BaptisteHudyma/Lamp-Da/Medias/circuit_flash_port.jpeg

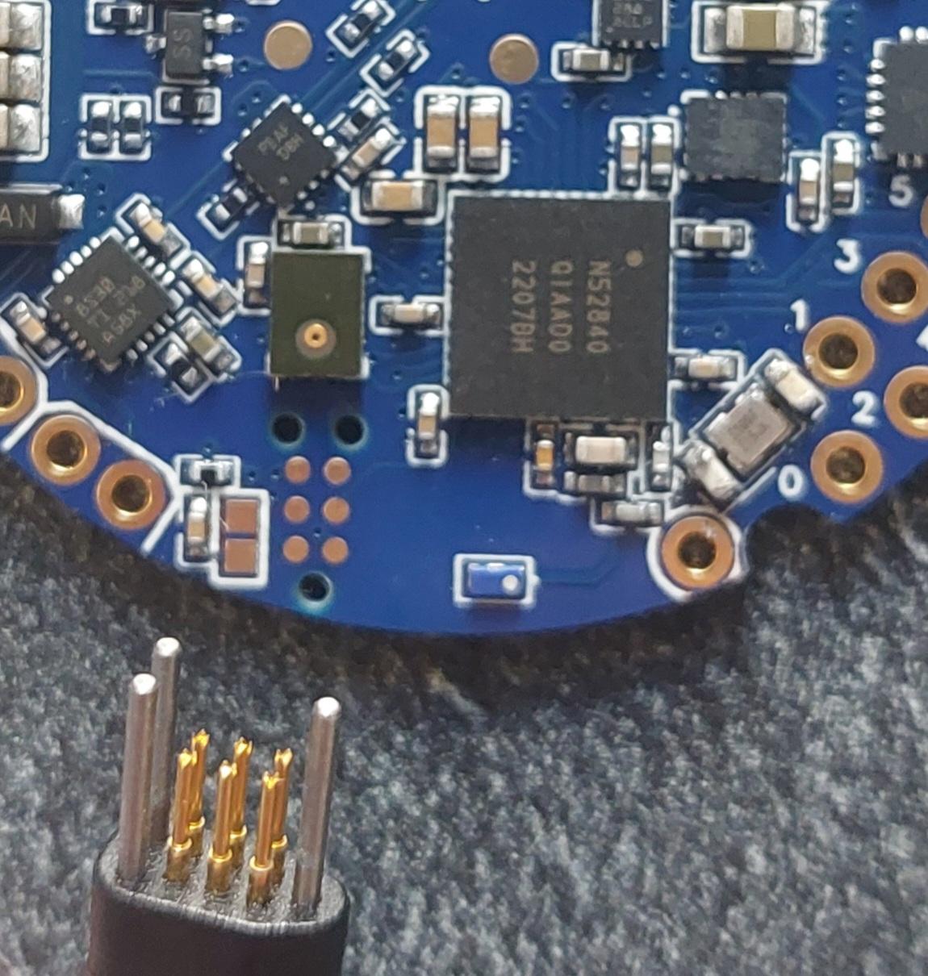
Medias/circuit_flash_port.jpeg
