BaptisteHudyma/Lamp-Da/Medias/Diagramme_commandes-Indexable.png

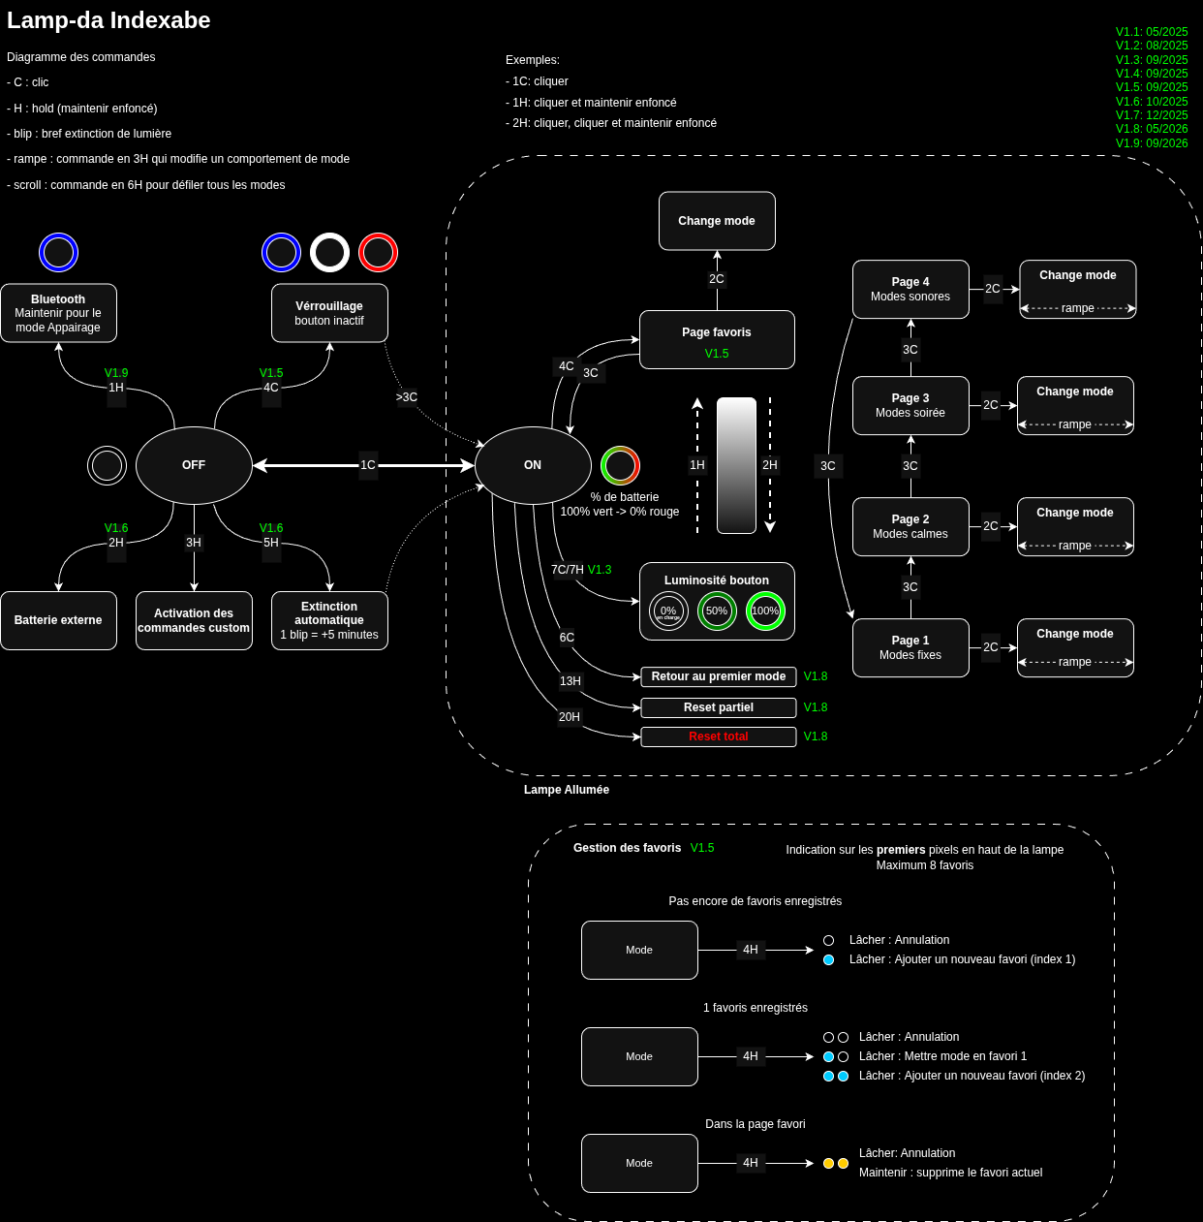
Medias/Diagramme_commandes-Indexable.png
