BaptisteHudyma/Lamp-Da/Medias/raspi_flasher.jpeg

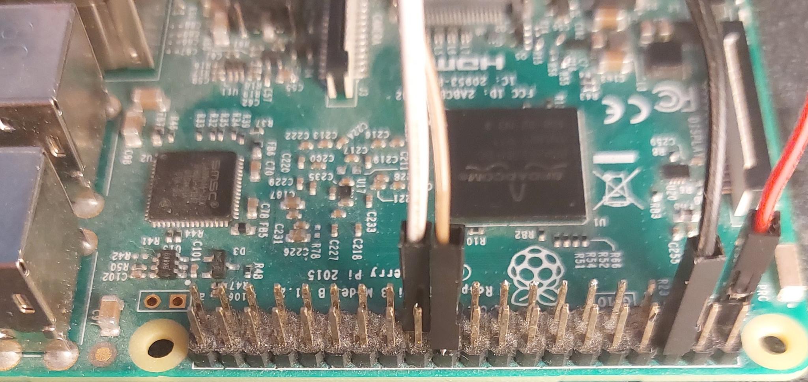
Medias/raspi_flasher.jpeg
