BaptisteHudyma/Lamp-Da/Medias/button_wiring.jpg

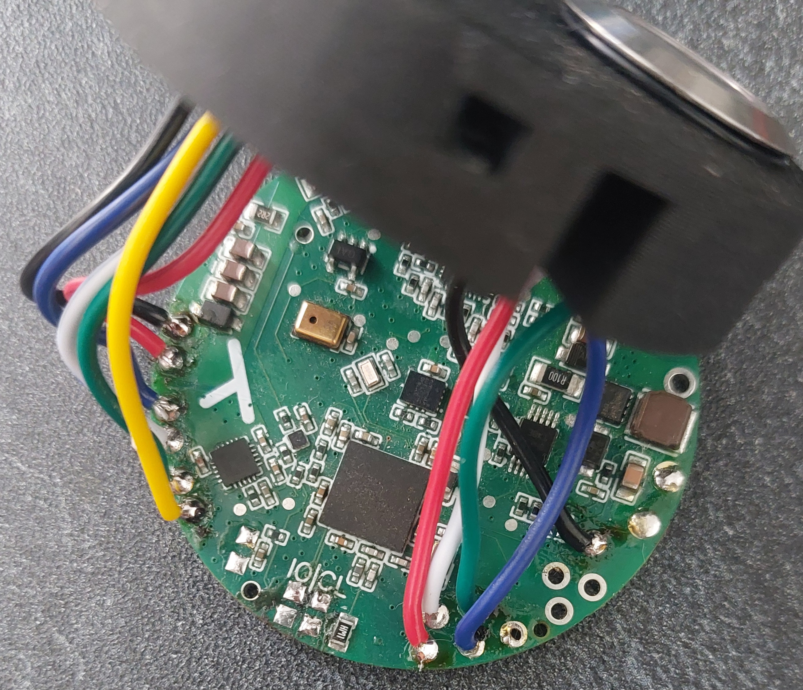
Medias/button_wiring.jpg
