BaptisteHudyma/Lamp-Da/Medias/full_assembly.png

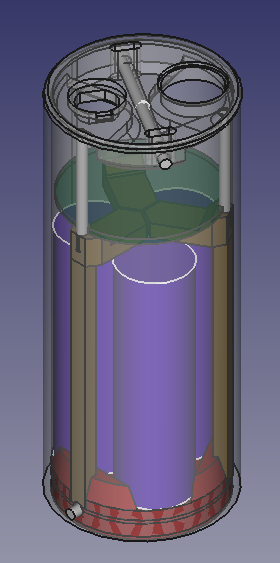
Medias/full_assembly.png
