BaptisteHudyma/Lamp-Da/Medias/printed_assembly.png

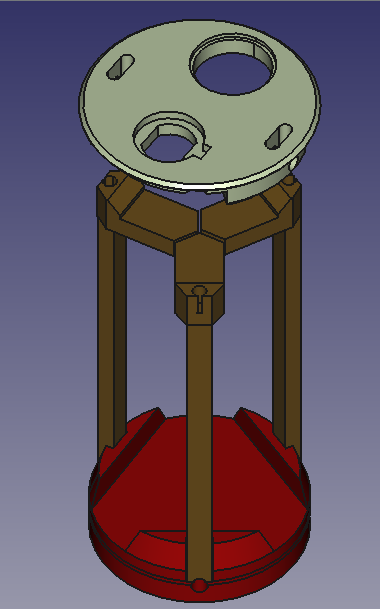
Medias/printed_assembly.png
