BaptisteHudyma/Lamp-Da/src/system/logic/behavior.cpp

#include "behavior.h"

#include <cstdint>

#include "src/system/ext/math8.h"
#include "src/system/ext/noise.h"

#include "src/system/hal/time.h"
#include "src/system/hal/gpio.h"
#include "src/system/hal/i2c.h"
#include "src/system/hal/registers.h"

#include "src/system/bsp/ble.h"
#include "src/system/bsp/text_out.h"

#include "src/system/logic/alerts.h"
#include "src/system/logic/inputs_bluetooth.h"
#include "src/system/logic/inputs.h"
#include "src/system/logic/statistics_handler.h"
#include "src/system/logic/power_handler.h"
#include "src/system/logic/sun_timers.h"

#include "src/system/bsp/indicator.h"
#include "src/system/bsp/filesystem.h"
#include "src/system/bsp/power_gates.h"
#include "src/system/bsp/threads.h"

#include "src/system/component/charger.h"
#include "src/system/component/battery.h"
#include "src/system/component/button.h"
#include "src/system/component/imu.h"
#include "src/system/component/output_power.h"
#include "src/system/component/sound.h"

#include "src/system/utils/colorspace.h"
#include "src/system/utils/constants.h"
#include "src/system/utils/input_output.h"
#include "src/system/utils/time_utils.h"
#include "src/system/utils/utils.h"

#include "src/system/common/state_machine.h"

#include "src/user/functions.h"

namespace lampda {
namespace logic {
namespace behavior {

static constexpr uint32_t cleanSleepKey = utils::hash("cleanSleep");
static constexpr uint32_t brightnessKey = utils::hash("brightness");
static constexpr uint32_t indicatorLevelKey = utils::hash("indLvl");
static constexpr uint32_t isLockoutModeKey = utils::hash("lckMode");
static constexpr uint32_t buttonPinKey = utils::hash("bttPin");
static constexpr uint32_t bluetoothAutoKey = utils::hash("ble");

// time to block turn off since turn on
static constexpr uint32_t SYSTEM_TURN_ON_ALLOW_TURN_OFF_DELAY = 500;
static constexpr uint32_t PRE_CHARGE_STATE_TIMEOUT_ms = 1000;
static constexpr uint32_t PRE_OUTPUT_STATE_TIMEOUT_ms = 1000;

/// bluetooth will power up automatically this number of next boots if user used it
static constexpr uint32_t maxBluetoothAutoActivations = 3;

// timestamp of the system wake up
static uint32_t wakeUpTime = 0;

// pre output light call timing (lamp output starts)
// Starts at system start time
static uint32_t preOutputLightCalled = 0;

// indicates that the system was waken up by voltage on vbus
static bool wokeUpFromVbus_s = false;
// indicates that the output should be turned on/off
static bool isTargetPoweredOn_s = false;
// indicates the error that started the error state
static etl::string<128> errorStateRaisedStr = "";
// indicates the time at which the pre-charge state started
static uint32_t preChargeCalled = 0;
// indicates the  time at which the output state is enabled
static uint32_t lastOutputLightValidTime = 0;
/// keep track of the number of auto bluetooth activation left
static uint32_t bluetoothAutoActivationLeftCount = 0;

// Define the state for the main prog state machine
using BehaviorStates = enum class behavior_t
{
  // handle the start logic
  START_LOGIC,

  // Prepare the charging operations
  PRE_CHARGER_OPERATION,
  // Charging, or usb OTG mode
  CHARGER_OPERATIONS,
  // Prepare the light operation
  PRE_OUTPUT_LIGHT,
  // output voltage on, light the led strip and enable user modes
  OUTPUT_LIGHT,
  // close the output safely
  POST_OUTPUT_LIGHT,

  // shutdown state (when set, the board wil shutdown)
  SHUTDOWN,

  // Should never happen, default state
  ERROR,
};
const char* BehaviorStatesStr[] = {
        "START_LOGIC",
        "PRE_CHARGER_OPERATION",
        "CHARGER_OPERATIONS",
        "PRE_OUTPUT_LIGHT",
        "OUTPUT_LIGHT",
        "POST_OUTPUT_LIGHT",
        "SHUTDOWN",
        "ERROR",
};
// main state machine
common::StateMachine<BehaviorStates> mainMachine(BehaviorStates::START_LOGIC);

// system was powered from vbus power event
bool did_woke_up_from_power() { return wokeUpFromVbus_s; }

// target power on state (not actual state)
bool is_system_should_be_powered() { return isTargetPoweredOn_s; }
void set_power_on() { isTargetPoweredOn_s = true; }
void set_power_off()
{
  // prevent early shutdown when system is just booting, or lamp jst turns on
  if (hal::time_ms() - preOutputLightCalled < SYSTEM_TURN_ON_ALLOW_TURN_OFF_DELAY)
    return;

  isTargetPoweredOn_s = false;
}

void go_to_external_battery_mode() { logic::power::go_to_otg_mode(); }

//
bool is_in_start_logic_state() { return mainMachine.get_state() == BehaviorStates::START_LOGIC; }
bool is_in_output_state() { return mainMachine.get_state() == BehaviorStates::OUTPUT_LIGHT; }
bool is_in_charge_state()
{
  return mainMachine.get_state() == BehaviorStates::CHARGER_OPERATIONS or
         mainMachine.get_state() == BehaviorStates::PRE_CHARGER_OPERATION;
}

namespace timers {

// signal update to user
void sunset_progress_update(const float progress) { user::sunset_timer_update(progress); }
void sunrise_progress_update(const float progress) { user::sunrise_timer_update(progress); }

} // namespace timers

// allow system to be powered if no hardware alert and power is setup
bool can_system_allowed_to_be_powered()
{
  return not(logic::alerts::manager.is_raised(logic::alerts::Type::SYSTEM_IN_ERROR_STATE) or
             not logic::power::is_setup());
}

// return true if vbus is high
bool is_charger_powered() { return ::lampda::component::charger::is_vbus_powered(); }

bool read_parameters()
{
  bool isSuccess = false;
  // load system values in memory
  if (not bsp::filesystem::system::load_from_file())
  {
    logic::alerts::manager.raise(logic::alerts::Type::SYSTEM_SLEEP_SKIPPED);
  }
  else
  {
    isSuccess = true;
    // load statistics first
    statistics::load_from_memory();

    uint32_t wasPutToSleepCleanly = 0;
    const bool isCleanFlagFound = bsp::filesystem::system::get_value(cleanSleepKey, wasPutToSleepCleanly);
    if (not isCleanFlagFound or wasPutToSleepCleanly != 0xDEADBEEF)
    {
      // dirty sleep alert
      logic::alerts::manager.raise(logic::alerts::Type::SYSTEM_SLEEP_SKIPPED);
    }

    uint32_t brightness = 0;
    if (bsp::filesystem::system::get_value(brightnessKey, brightness))
    {
      logic::brightness::update_brightness(brightness, true);
      logic::brightness::update_saved_brightness();
    }

    uint32_t indicatorLevel = 0;
    if (bsp::filesystem::system::get_value(indicatorLevelKey, indicatorLevel))
    {
      logic::indicator::set_brightness_level(indicatorLevel);
    }

    uint32_t isInLockoutMode = 0;
    if (bsp::filesystem::system::get_value(isLockoutModeKey, isInLockoutMode) and isInLockoutMode != 0)
    {
      // system in lockout, raise the alert
      logic::alerts::manager.raise(logic::alerts::Type::SYSTEM_IN_LOCKOUT);
    }

    uint32_t buttonPin = 0;
    if (bsp::filesystem::system::get_value(buttonPinKey, buttonPin) and buttonPin > 0)
    {
      component::button::set_button_pin(static_cast<hal::gpio::DigitalPin::GPIO>(buttonPin));
    }

    // Auto activate bluetooth is needed
    uint32_t bluetoothAutoActivation = 0;
    if (bsp::filesystem::system::get_value(bluetoothAutoKey, bluetoothAutoActivation) and bluetoothAutoActivation > 0)
    {
      bluetoothAutoActivationLeftCount = min<uint32_t>(maxBluetoothAutoActivations, bluetoothAutoActivation - 1);

      // bounded device, advertize but only allow the bounded device, if it exist
      bsp::ble::start_advertising(false);
    }
    else
    {
      bluetoothAutoActivationLeftCount = 0;
    }
  }

  if (not bsp::filesystem::user::load_from_file())
  {
    // We can live without the user parameters, but log it
    bsp::lampda_print("ERROR: Failed to read user parameters");
  }

  // Load the user anyway, there is a default parameter logic in here
  user::read_parameters();

  return isSuccess;
}

void setup_clean_sleep_flag()
{
  // clear clean sleep flag
  bsp::filesystem::system::set_value(cleanSleepKey, 0);
  // write parameters, if a crash happens, we will notice a dirty flag
  bsp::filesystem::system::write_to_file();
}

void write_parameters()
{
  bsp::filesystem::user::clear_cached();

  // write updated statistics
  statistics::write_to_memory();

  bsp::filesystem::system::set_value(cleanSleepKey, 0xDEADBEEF);
  // only save saved brightness, not current
  bsp::filesystem::system::set_value(brightnessKey, logic::brightness::get_saved_brightness());
  bsp::filesystem::system::set_value(indicatorLevelKey, logic::indicator::get_brightness_level());
  // lockout mode always kept, if not deactivated by system
  bsp::filesystem::system::set_value(isLockoutModeKey,
                                     logic::alerts::manager.is_raised(logic::alerts::Type::SYSTEM_IN_LOCKOUT));
  bsp::filesystem::system::set_value(buttonPinKey, static_cast<uint32_t>(component::button::get_button_pin()));

  // if the user used the bluetooth, it will be written here for auto activation
  const uint32_t nextWakeUpWithBluetooth =
          logic::inputs_bluetooth::is_bluetooth_used() ? maxBluetoothAutoActivations : bluetoothAutoActivationLeftCount;
  bsp::filesystem::system::set_value(bluetoothAutoKey, nextWakeUpWithBluetooth);

  // write user parameters
  user::write_parameters();

  // write all
  bsp::filesystem::user::write_to_file();
  bsp::filesystem::system::write_to_file();
}

// user code is running when state is output
bool is_user_code_running() { return mainMachine.get_state() == BehaviorStates::OUTPUT_LIGHT; }

void set_error_state_message(const etl::string<128>& errorMsg)
{
  if (errorStateRaisedStr.empty())
  {
    errorStateRaisedStr = etl::string<128>("\n\t").append(errorMsg);
  }
}
etl::string<128> get_error_state_message()
{
  if (errorStateRaisedStr.empty())
    return "x";
  return errorStateRaisedStr;
}

void go_to_error_state(const etl::string<128>& errorMsg)
{
  statistics::signal_output_off();

  // signal to the system we dont want to turn off until user asked
  // thats better to debug an error
  set_power_on();
  // set error msg
  set_error_state_message(errorMsg);
  // got to error state
  mainMachine.set_state(BehaviorStates::ERROR);
}

namespace internal {

void handle_error_state()
{
  set_error_state_message("Unspecified raised error state reason");

  // not allowed to start, can only be stopped
  // turn off system is needed
  if (not is_system_should_be_powered())
  {
    // got to sleep after the closing operations
    mainMachine.set_state(BehaviorStates::SHUTDOWN);
  }

  // power states go to error too
  logic::power::go_to_error();

  // kick power and user watchdog (prevent reset)
  hal::registers::kick_watchdog(POWER_WATCHDOG_ID);
  hal::registers::kick_watchdog(USER_WATCHDOG_ID);

  // if error state, raise alert
  logic::alerts::manager.raise(logic::alerts::Type::SYSTEM_IN_ERROR_STATE);
}

void handle_start_logic_state()
{
  // set clean flag early on
  setup_clean_sleep_flag();

  // prevent early charging
  logic::power::enable_charge(false);

  // safety for failure of components at startup
  if (not can_system_allowed_to_be_powered())
  {
    go_to_error_state("system not allowed to power on in start logic state");
    return;
  }
  if (logic::power::is_in_error_state())
  {
    go_to_error_state("power system in error state in start logic state");
    return;
  }
  if (not logic::power::is_started())
  {
    // wait until power is started
    hal::delay_ms(1);
    return;
  }

  //
  if (did_woke_up_from_power())
  {
    // signal to the alert manager that we started by power input
    logic::alerts::signal_wake_up_from_charger();

    // start the charge operation
    mainMachine.set_state(BehaviorStates::PRE_CHARGER_OPERATION);
  }
  else
  {
    // small hack: the first button click is never registered, because it happens before the system boots
    set_power_on();
    // start the system normally
    mainMachine.set_state(BehaviorStates::PRE_OUTPUT_LIGHT);
  }
}

void handle_pre_charger_operation_state()
{
  if (logic::power::is_in_error_state())
  {
    go_to_error_state("power system in error state in pre charger operation state");
    return;
  }
  if (hal::time_ms() - mainMachine.get_state_raised_time() > PRE_CHARGE_STATE_TIMEOUT_ms)
  {
    go_to_error_state("pre charger operation failed to toggle to charge");
    return;
  }

  preChargeCalled = hal::time_ms();

  if (not component::battery::can_battery_be_charged())
  {
    // battery cannot be charged
    return;
  }
  if (not logic::alerts::manager.can_use_usb_port())
  {
    // USB port use is locked
    return;
  }

  // force OTG
  if (not logic::power::is_in_otg_mode())
    logic::power::go_to_charger_mode();
  mainMachine.set_state(BehaviorStates::CHARGER_OPERATIONS);
}

void handle_charger_operation_state()
{
  if (logic::power::is_in_error_state())
  {
    go_to_error_state("power system in error state in charger operation state");
    return;
  }

  // pressed the start button, stop charge and start lamp
  if (is_system_should_be_powered())
  {
    // forbid charging
    logic::power::enable_charge(false);
    bsp::threads::yield_this_thread();

    // switch to output mode after the post charge operations
    mainMachine.set_state(BehaviorStates::PRE_OUTPUT_LIGHT);
    return;
  }

  // clear lockout in charge mode
  logic::alerts::manager.clear(logic::alerts::Type::SYSTEM_IN_LOCKOUT);

  // wait a bit after going to charger mode, maybe vbus is bouncing around
  const bool vbusDebounced =
          ::lampda::component::charger::can_use_vbus_power() or (hal::time_ms() - preChargeCalled) > 5000;
  if (vbusDebounced)
  {
    static uint32_t otgDebounce_time = 0;
    if (::lampda::component::charger::get_state().isInOtg)
    {
      otgDebounce_time = hal::time_ms();
    }

    // otg mode
    if ((otgDebounce_time != 0) and (hal::time_ms() - otgDebounce_time) <= 500)
    {
      // do nothing (for now !)
    }
    // no power, shutdown everything
    else if (not is_charger_powered())
    {
      // forbbid charging
      logic::power::enable_charge(false);
      bsp::threads::yield_this_thread();

      // go to sleep after closing the charger
      mainMachine.set_state(BehaviorStates::SHUTDOWN);
      return;
    }
    else
    {
      // enable charge after the debounce
      logic::power::enable_charge(true);
    }
  }
  // else: ignore all
}

bool check_handle_exit_output_mode()
{
  // should go to sleep
  if (not is_system_should_be_powered())
  {
    // cancel both
    logic::sun_timers_cancel_all();

    if (is_charger_powered())
    {
      // charger is plugged, go to charger state
      mainMachine.set_state(BehaviorStates::POST_OUTPUT_LIGHT, 100, BehaviorStates::PRE_CHARGER_OPERATION);
    }
    else
    {
      // got to sleep after the closing operations
      mainMachine.set_state(BehaviorStates::POST_OUTPUT_LIGHT, 1000, BehaviorStates::SHUTDOWN);
    }
    return true;
  }
#ifndef LMBD_SIMULATION
  else if (not component::battery::is_battery_usable_as_power_source())
  {
    logic::sunset_timer.cancel();

    // wait a bit then shutdown
    if (hal::time_ms() - preOutputLightCalled > 3000)
    {
      // indicate we should power the systemm off
      set_power_off();
    }
    return true;
  }
#endif

  return false;
}

void handle_pre_output_light_state()
{
  static bool isMessageDisplayed = false;

  if (logic::power::is_in_error_state())
  {
    go_to_error_state("power system in error state in pre output light state");
    return;
  }
  if (hal::time_ms() - mainMachine.get_state_raised_time() > PRE_OUTPUT_STATE_TIMEOUT_ms)
  {
    go_to_error_state("pre output operation failed to toggle");
    return;
  }

  // power usage is forbidden
  if (not component::battery::is_battery_usable_as_power_source())
  {
    if (not isMessageDisplayed)
    {
      bsp::lampda_print("no output allowed");
      isMessageDisplayed = true;
    }
    // check if we may go to sleep
    check_handle_exit_output_mode();
    return;
  }

  if (logic::alerts::manager.is_raised(logic::alerts::Type::SYSTEM_IN_LOCKOUT))
  {
    if (not isMessageDisplayed)
    {
      bsp::lampda_print("not output in lockout state");
      isMessageDisplayed = true;
    }
    // check if we may go to sleep
    check_handle_exit_output_mode();
    return;
  }

  //
  isMessageDisplayed = false;

  // critical battery level, do not wake up
  if (component::battery::get_battery_minimum_cell_level() <= batteryCritical + 1)
  {
    // alert user of low battery
    for (uint8_t i = 0; i < 10; i++)
    {
      bsp::indicator::set_color(utils::ColorSpace::RED);
      hal::delay_ms(100);
      bsp::indicator::set_color(utils::ColorSpace::BLACK);
      hal::delay_ms(100);
    }

    if (is_charger_powered())
    {
      // go to battery charge instead of shutdown
      isTargetPoweredOn_s = false;
      mainMachine.set_state(BehaviorStates::PRE_CHARGER_OPERATION);
    }
    else
    {
      // battery too low to be powered
      mainMachine.set_state(BehaviorStates::SHUTDOWN);
    }
    return;
  }
  preOutputLightCalled = hal::time_ms();

  logic::power::go_to_output_mode();

  // update brightness with saved brightness
  logic::brightness::update_brightness(logic::brightness::get_saved_brightness());

  // let the user power on the system
  user::power_on_sequence();

  lastOutputLightValidTime = hal::time_ms();

  // this function is executed ONCE
  statistics::signal_output_on();
  mainMachine.set_state(BehaviorStates::OUTPUT_LIGHT);
}

void handle_output_light_state()
{
  if (logic::power::is_in_error_state())
  {
    go_to_error_state("power system in error state in output light state");
    return;
  }

  // shortcut to external battery mode
  if (logic::power::is_in_otg_mode())
  {
    // ignore timing, special case
    isTargetPoweredOn_s = false;
    mainMachine.set_state(BehaviorStates::POST_OUTPUT_LIGHT, 100, BehaviorStates::PRE_CHARGER_OPERATION);
    return;
  }

  static bool waitingForPowerGate_messageDisplayed = true;

  // wait for power gates (and display message when ready)
  if (not ::lampda::bsp::powergates::is_power_gate_enabled() or not logic::power::is_output_mode_ready())
  {
    if (waitingForPowerGate_messageDisplayed)
    {
      bsp::lampda_print("Behavior>Output mode: waiting for power gate");
      waitingForPowerGate_messageDisplayed = false;
    }

    if (hal::time_ms() - lastOutputLightValidTime > 1000)
    {
      etl::string<128> errStr("power gate took too long to switch in output light state ");
      errStr.push_back(static_cast<char>(::lampda::bsp::powergates::is_power_gate_enabled()));
      errStr.push_back(static_cast<char>(logic::power::is_output_mode_ready()));
      go_to_error_state(errStr);
    }
    return;
  }
  waitingForPowerGate_messageDisplayed = true;

  lastOutputLightValidTime = hal::time_ms();

  // normal running loop
  if (not check_handle_exit_output_mode())
  {
    // resume secondary thread
    if (user::should_spawn_thread())
      bsp::threads::resume_thread(bsp::threads::user_taskName);

    // user loop call
    user::loop();

    const auto& chargerState = ::lampda::component::charger::get_state();
    if (chargerState.status == ::lampda::component::charger::Charger_t::ChargerStatus_t::ERROR_BATTERY_MISSING)
    {
      logic::alerts::manager.raise(logic::alerts::Type::BATTERY_MISSING);
    }
  }
}

void handle_post_output_light_state()
{
  // button usermode is kept disabled
  inputs::button_disable_usermode();

  // let the user power off the system
  user::power_off_sequence();
  // write/stability delay
  hal::delay_ms(10);

  // deactivate strip power
  component::outputPower::disable_power_gates(); // close external voltage path
  hal::delay_ms(1);
  component::outputPower::write_voltage(0); // power down

  statistics::signal_output_off();
  mainMachine.skip_timeout();
}

void handle_shutdown_state()
{
  statistics::signal_output_off();

  /**
   * Software shutdown phase
   */

  // Phase 1: bluetooth & com shutdown
  component::button::shutdown();          ///< prevent more button commands
  bsp::ble::stop_bluetooth_advertising(); ///< stop bluetooth
  bsp::ble::shutdown();                   ///< deactivate bluetooth
  hal::delay_ms(20);

  // Phase 2: peripheral shutdown
  component::microphone::disable();
  component::imu::shutdown();
  component::outputPower::write_voltage(0); // power down
  hal::delay_ms(10);

  // Phase 3: power / filesystem
  if (not logic::power::go_to_shutdown())
  {
    // TODO: error ?
  }
  // save the current config to a file
  write_parameters();
  hal::delay_ms(20);
  bsp::filesystem::shutdown();

  // Phase 4: Stop I2C
  for (uint8_t i = 0; i < hal::registers::get_wire_interface_count(); ++i)
  {
    hal::i2c::i2c_turn_off(i);
  }
  hal::delay_ms(10);

  // Phase 5: disable interrupts
  hal::gpio::DigitalPin::detach_all();
  hal::delay_ms(5);

  // Phase 6: Shutdown threads & task stack
  bsp::threads::shutdown();
  hal::delay_ms(10);

  // Phase 7: GPIO deactivation
  // deactivate indicator
  bsp::indicator::set_color(utils::ColorSpace::BLACK);
  hal::delay_ms(1);
  // disable peripherals
  hal::gpio::DigitalPin(hal::gpio::DigitalPin::GPIO::Output_EnableExternalPeripherals).set_high(false);
#ifdef IS_HARDWARE_1_0
  // disable pullup in sleep mode (in V>1.0, done electrically)
  hal::gpio::DigitalPin(hal::gpio::DigitalPin::GPIO::Input_isChargeOk)
          .set_pin_mode(hal::gpio::DigitalPin::Mode::kInput);
  hal::gpio::DigitalPin(hal::gpio::DigitalPin::GPIO::Signal_BatteryBalancerAlert)
          .set_pin_mode(hal::gpio::DigitalPin::Mode::kInput);
#endif
  // disable gates
  hal::gpio::DigitalPin(hal::gpio::DigitalPin::GPIO::Output_EnableVbusGate).set_high(false);
  hal::gpio::DigitalPin(hal::gpio::DigitalPin::GPIO::Output_EnableOutputGate).set_high(false);
  hal::gpio::DigitalPin::deactivate_gpios(); // physically disconnect gpios
  hal::delay_ms(10);

  // Phase 8 : Sleep with wakeup config

  hal::registers::sync_memory_protection();

  // If button is still pressed at this point, we will assume it is stuck pressed and signal a wakeup on release.
  const bool isButtonPressed = component::button::get_button_state().isPressed;
  // power down nrf52.
  // on wake up, it'll start back from the setup phase
  hal::registers::go_to_sleep(component::button::get_button_pin_RAW(), isButtonPressed);

  /*
   * Nothing after this, system is off !
   */

  // if we reach this, the system failed to go to sleep, registers may be broken
  logic::alerts::manager.raise(logic::alerts::Type::SYSTEM_OFF_FAILED);
  go_to_error_state("system failed to sleep");
}

uint32_t get_bluetooth_auto_activation_left() { return bluetoothAutoActivationLeftCount; }

} // namespace internal

/// Handle the behavior states
void state_machine_behavior()
{
  mainMachine.run();
  // if state changed, display the new state
  if (mainMachine.state_just_changed())
  {
    bsp::lampda_print("BEHAVIOR_S_MACH > switched to state %s",
                      BehaviorStatesStr[static_cast<size_t>(mainMachine.get_state())]);
  }

  switch (mainMachine.get_state())
  {
    // strange error state
    case BehaviorStates::ERROR:
      internal::handle_error_state();
      break;
    // called when system starts
    case BehaviorStates::START_LOGIC:
      internal::handle_start_logic_state();
      break;
    // prepare the charger operation
    case BehaviorStates::PRE_CHARGER_OPERATION:
      internal::handle_pre_charger_operation_state();
      break;
    // charge batteries, or power OTG on USB-port
    case BehaviorStates::CHARGER_OPERATIONS:
      internal::handle_charger_operation_state();
      break;
    // prepare the output light
    case BehaviorStates::PRE_OUTPUT_LIGHT:
      internal::handle_pre_output_light_state();
      break;
    // output current to system, handle user inputs
    case BehaviorStates::OUTPUT_LIGHT:
      internal::handle_output_light_state();
      break;
    case BehaviorStates::POST_OUTPUT_LIGHT:
      internal::handle_post_output_light_state();
      break;
    case BehaviorStates::SHUTDOWN:
      internal::handle_shutdown_state();
      break;
    default:
      {
        go_to_error_state("reached state machine default state");
      }
      break;
  }
}

// system was powered by vbus high event
void set_woke_up_from_vbus(const bool wokeUp) { wokeUpFromVbus_s = wokeUp; }

// main behavior loop
void loop()
{
  state_machine_behavior();

  // do not display alerts for the first 500 ms
  const bool shouldIgnoreAlerts = (hal::time_ms() - wakeUpTime) < 500;
  logic::alerts::handle_all(shouldIgnoreAlerts);
  // alert requested an emergency shutdown, do it
  if (logic::alerts::is_request_shutdown())
  {
    bsp::lampda_print("emergency shutdown from alert");
    // just in case, turn off eventual states
    internal::handle_post_output_light_state();
    // shutdown normally
    internal::handle_shutdown_state();
  }

  // only handle those when system is not in alert state
  if (mainMachine.get_state() == BehaviorStates::PRE_OUTPUT_LIGHT or
      mainMachine.get_state() == BehaviorStates::OUTPUT_LIGHT)
  {
    // at any point when the alert is raised, got to power off
    if (logic::alerts::manager.is_raised(logic::alerts::Type::SYSTEM_IN_LOCKOUT) and
        logic::alerts::manager.get_time_since_raised(logic::alerts::Type::SYSTEM_IN_LOCKOUT) > 950)
    {
      const auto& buttonState = component::button::get_button_state();
      const bool isButtonPressed = buttonState.isPressed or buttonState.isLongPressed;
      // shutdown with button pressed starts right back up.
      if (not isButtonPressed)
        behavior::set_power_off();
    }
  }
}

etl::string<32> get_state() { return etl::string<32>(BehaviorStatesStr[static_cast<size_t>(mainMachine.get_state())]); }

} // namespace behavior
} // namespace logic
} // namespace lampda

//
// do not modify (if you do not understand it)
//

#ifdef LMBD_CPP17

const char* ensure_build_canary()
{
#warning "compiling ensure_build_canary"

#ifdef LMBD_LAMP_TYPE__SIMPLE
  return "_lmbd__build_canary__simple";
#endif
#ifdef LMBD_LAMP_TYPE__CCT
  return "_lmbd__build_canary__cct";
#endif
#ifdef LMBD_LAMP_TYPE__INDEXABLE
  return "_lmbd__build_canary__indexable";
#endif
  return (char*)nullptr;
}

#endif
