BaptisteHudyma/Lamp-Da/src/modes/include/hardware/lamp_type.hpp

/*! \file lamp_type.hpp
    \brief Define the main led strip interaction object.
*/

#ifndef MODES_HARDWARE_LAMP_TYPE_HPP
#define MODES_HARDWARE_LAMP_TYPE_HPP

#include <cstdint>
#include <cstring>

#include "src/compile.h"
#include "src/user/constants.h"

#include "src/system/component/output_power.h"
#include "src/system/component/sound.h"

#ifdef LMBD_LAMP_TYPE__INDEXABLE
#include "src/system/component/strip.h"
#endif

#include "src/system/hal/time.h"

#include "src/system/bsp/text_out.h"

#include "src/system/logic/brightness_handle.h"

#include "src/system/utils/assert.h"
#include "src/system/utils/constants.h"
#include "src/system/utils/utils.h"

#include "src/system/common/curves.h"

#include "src/system/ext/math8.h"

#include "src/modes/include/compile.hpp"
#include "src/modes/include/hardware/coordinates.hpp"

#include "src/modes/include/colors/utils.hpp"
#include "src/modes/include/colors/palettes.hpp"

namespace lampda::modes {

struct XYTy
{
  uint16_t x; ///< x 2D led grid coordinates
  uint16_t y; ///< y 2D led grid coordinates
};

/// convert grid coordinates to strip index
static constexpr uint16_t to_strip(uint16_t, uint16_t);
/// convert strip index to grid coordinates
static constexpr XYTy strip_to_XY(uint16_t n);

struct HelixXYZTy
{
  float x; ///< x 3D mm coordinates
  float y; ///< y 3D mm coordinates
  float z; ///< z 3D mm coordinates
};

/// convert strip index to 3D coordinates
static constexpr HelixXYZTy strip_to_helix(int16_t n);

/// convert strip index to 3D coordinates, without checks on led index.
/// This allows to use 3D coordinates out of the lamp body
static constexpr HelixXYZTy strip_to_helix_unconstraint(const int16_t n);
/// True if the given strip index is a valid one
static constexpr bool is_led_index_valid(const int16_t ledIndex);
/// True if the given led index is out of bounds
static constexpr bool is_lamp_coordinate_out_of_bounds(const float angle_rad, const float z);

/**
 * \brief convert a lamp coordinate to a led index
 */
static constexpr uint16_t to_led_index(const float angle_rad, const float z);

/**
 * \brief convert a lamp coordinate to a led index, the result can be an index out of the lamp body
 */
static constexpr int16_t to_led_index_no_bounds(const float angle_rad, const float z);

} // namespace lampda::modes

/// Provide interface to the physical hardware and other facilities
namespace lampda::modes::hardware {

/** \brief Enumeration to write code working with all lamp types
 *
 * See LampTy::flavor and its usage
 */
enum class LampTypes : uint8_t
{
  simple,    ///< Equivalent to LMBD_LAMP_TYPE__SIMPLE
  cct,       ///< Equivalent to LMBD_LAMP_TYPE__CCT
  indexable, ///< Equivalent to LMBD_LAMP_TYPE__INDEXABLE
};

#ifdef LMBD_LAMP_TYPE__SIMPLE
static constexpr LampTypes _lampType = LampTypes::simple;
#endif

#ifdef LMBD_LAMP_TYPE__CCT
static constexpr LampTypes _lampType = LampTypes::cct;
#endif

#ifdef LMBD_LAMP_TYPE__INDEXABLE
static constexpr LampTypes _lampType = LampTypes::indexable;
#endif

/// Currently implemented lamp type, defined at compile-time by the user
static constexpr LampTypes lampType = _lampType;

/** \brief Main interface between the user and the hardware of the lamp
 *
 * TODO: write recipes for best practices when doing Simple/CCT/Indexable
 */
struct LampTy
{
  //
  // state managed by manager
  //

  /// Store a display config
  struct LampConfig
  {
    uint16_t skipFirstLedsForEffect = 0; ///< Skip duration
    uint16_t skipFirstLedsForAmount = 0; ///< Skip the first N leds
  };

  /// store a display configuration
  LampConfig config;

  //
  // private constructors
  //

#ifdef LMBD_LAMP_TYPE__INDEXABLE
private:
  static constexpr float _fwidth = stripXCoordinates;                    ///< \private
  static constexpr float _fheight = stripYCoordinates;                   ///< \private
  static constexpr uint16_t _width = floor(_fwidth);                     ///< \private
  static constexpr uint16_t _height = floor(_fheight);                   ///< \private
  static constexpr uint16_t _ledCount = LED_COUNT;                       ///< \private
  static constexpr uint16_t _nbBuffers = stripNbBuffers;                 ///< \private
  static constexpr float _lampBodyRadius_mm = lampda::lampBodyRadius_mm; ///< \private
  static constexpr float _ledStripWidth_mm = lampda::ledStripWidth_mm;   ///< \private
  static constexpr float _ledStripLength_mm = lampda::ledStripLength_mm; ///< \private
  static constexpr float _ledByMeter = lampda::ledByMeter;               ///< \private
  component::LedStrip& strip;                                            ///< \private

  /// \private oversized buffer size to account for "overflowing" LEDs
  static constexpr uint16_t _safeBufSize = (_width + 1) * (_height + 1);

  /// Type for a uint32_t buffer of exactly ledCount length
  using BufferTy = std::array<uint32_t, _ledCount>;
  // using BufferTy = std::array<uint32_t, _safeBufSize>;

  LampTy() = delete;                         ///< \private
  LampTy(const LampTy&) = delete;            ///< \private
  LampTy& operator=(const LampTy&) = delete; ///< \private

public:
  /// \private Constructor used to wrap strip if needed
  LMBD_INLINE LampTy(component::LedStrip& strip) : config {}, strip {strip}, now {0}, tick {0}, raw_frame_count {0} {}
#else
private:
  // (placeholder values to avoid bad fails on misuse)
  static constexpr float _fwidth = 23.5451;          ///< \private
  static constexpr float _fheight = 22.51;           ///< \private
  static constexpr uint16_t _width = 23;             ///< \private
  static constexpr uint16_t _height = 22;            ///< \private
  static constexpr uint16_t _ledCount = 530;         ///< \private
  static constexpr uint16_t _nbBuffers = 3;          ///< \private
  static constexpr float _lampBodyRadius_mm = 25.0f; ///< \private
  static constexpr float _ledStripWidth_mm = 5.2f;   ///< \private
  static constexpr float _ledStripLength_mm = 25.0f; ///< \private
  static constexpr float _ledByMeter = 160.0f;       ///< \private

  /// \private oversized buffer size to account for "overflowing" LEDs
  static constexpr uint16_t _safeBufSize = (_width + 1) * (_height + 1);

  /// Type for a uint32_t buffer of exactly ledCount length
  using BufferTy = std::array<uint32_t, _ledCount>;
  // using BufferTy = std::array<uint32_t, _safeBufSize>;

  LampTy(const LampTy&) = delete;            ///< \private
  LampTy& operator=(const LampTy&) = delete; ///< \private

  struct LedStrip ///< \private
  {
    BufferTy _buffers[_nbBuffers];
    COLOR _colors[_ledCount]; // !! slighly smaller than buffers in _buffers !!

    void begin();
    void show();
    void show_now();
    void signal_display();
    void setBrightness(brightness_t);
    uint8_t getBrightness();
    void setPixelColor(uint16_t, uint32_t);
    uint32_t getPixelColor(uint16_t);
  };
  LedStrip fakeStrip; ///< \private
  LedStrip& strip;    ///< \private

public:
  /// \private Constructor used to wrap strip if needed
  LMBD_INLINE LampTy() : config {}, fakeStrip {}, strip {fakeStrip}, now {0}, tick {0}, raw_frame_count {0} {}
#endif

  //
  // private API
  //

  /// \private (refresh internal const tick variable)
  void LMBD_INLINE refresh_tick_value()
  {
    uint32_t* writeable_now = const_cast<uint32_t*>(&now);
    *writeable_now = hal::time_ms();

    uint32_t* writable_tick = const_cast<uint32_t*>(&tick);
    *writable_tick = now / frameDurationMs;

    uint32_t* writable_frame_count = const_cast<uint32_t*>(&raw_frame_count);
    *writable_frame_count += 1; // monotonous
  }

  /** \private Startup sequence of the lamp from a powered-off state
   *
   * In order:
   *  - call lamp.begin()
   *  - call lamp.clear()
   *  - call lamp.show()
   *  - call lamp.setBrightness(get_brightness(), true, true)
   *
   * Supports all flavors, even if most steps are no-op if not indexable
   */
  void LMBD_INLINE startup()
  {
    // set output voltage for leds that will not change voltage
    if (stripInputMinVoltage_mV == stripInputMaxVoltage_mV)
      component::outputPower::write_voltage(stripInputMaxVoltage_mV);

    begin();
    clear();
    show_now();
    setBrightness(logic::brightness::get_saved_brightness(), true, true);
    align_internal_to_system_brightness();
  }

  /** \private Does necessary work to setup lamp from a powered-off state
   *
   * If flavor is LampTypes::indexable then:
   *  - call the "begin" method of the LED strip to let it setup itself
   *
   * Or else, subject to change as other flavors are integrated:
   *  - does nothing
   */
  void LMBD_INLINE begin()
  {
    if constexpr (flavor == LampTypes::indexable)
    {
      strip.begin();
    }
    else
    {
      // (this is optimized out, and is essentially no-op for other flavors)
      assert(true);
    }
  }

  /** \private Does necessary work to display not-yet-shown lamp changes
   *
   * If LampTy::flavor is LampTypes::indexable then:
   *  - update the output of the lamp with currently buffered changes
   *
   * Or else, subject to change as other flavors are integrated:
   *  - does nothing
   */
  void LMBD_INLINE show()
  {
    if constexpr (flavor == LampTypes::indexable)
    {
      strip.show();
    }
    else
    {
      // (this is optimized out, and is essentially no-op for other flavors)
      assert(true);
    }
  }

  /** \private Does necessary work to display not-yet-shown lamp changes
   *
   * If LampTy::flavor is LampTypes::indexable then:
   *  - update the output of the lamp with currently buffered changes IMMEDIATLY
   *
   * Or else, subject to change as other flavors are integrated:
   *  - does nothing
   */
  void LMBD_INLINE show_now()
  {
    if constexpr (flavor == LampTypes::indexable)
    {
      strip.show_now();
    }
    else
    {
      // (this is optimized out, and is essentially no-op for other flavors)
      assert(true);
    }
  }

  /** \private Signal to underlying strip that things are ready to be displayed
   *
   * If LampTy::flavor is LampTypes::indexable then:
   *  - call the .signal_display() method of the underlying strip object
   *
   * Or else, subject to change as other flavors are integrated:
   *  - does nothing
   */
  void LMBD_INLINE signal_display()
  {
    if constexpr (flavor == LampTypes::indexable)
    {
      strip.signal_display();
    }
    else
    {
      // (this is optimized out, and is essentially no-op for other flavors)
      assert(true);
    }
  }

  //
  // public constants
  //

  /// Which lamp flavor is currently used by the implementation?
  static constexpr LampTypes flavor = lampType;

  /// Hardward try to call .loop() every frameDurationMs (12ms for 83.3fps)
  static constexpr uint32_t frameDurationMs = MAIN_LOOP_UPDATE_PERIOD_MS;

#ifndef LMBD_LAMP_TYPE__INDEXABLE_IS_HD
  // (we have 12ms and 83.3fps values to be updated in this file)
  static_assert(frameDurationMs == 12, "Update the documentation of .tick :)");
#endif

  /// Limit mode-requested brightness changes to one every few frames
  static constexpr uint32_t brightnessDurationMs = frameDurationMs * 2;

  /** \brief (indexable) Count of indexable LEDs on the lamp
   *
   * Equal to \p LED_COUNT if LampTypes::indexable or else 512
   */
  static constexpr uint16_t ledCount = _ledCount;

  /** \brief (indexable) Width of "pixel space" w/ lamp taken as a LED matrix
   *
   * This width equals the smallest maximal X coordinate for which all rows
   * are fully displayed on the lamp taken as an "XY-display" LED matrix.
   *
   * All rows are of length of at least \p maxWidth but some will be of length
   * \p maxOverflowWidth depending on the exact diameter of the lamp and
   * density of the LED strip.
   *
   * Equal to \p stripXCoordinates (floor) if LampTypes::indexable or else 23
   */
  static constexpr uint16_t maxWidth = _width;

  /// Width as a precise floating point number, equal to \p stripXCoordinates
  static constexpr float maxWidthFloat = _fwidth;

  /// Larger width, taken as the absolute maximum X coordinate on all rows
  static constexpr uint16_t maxOverflowWidth = maxWidth + 1;

  /** \brief (indexable) Height of "pixel space" w/ lamp taken as a LED matrix
   *
   * This height equals the largest Y coordinate for which a full \p maxWidth
   * row can be displayed, the last row at coordinate \p maxOverflowHeight
   * being likely to be truncated depending on the exact diameter of the lamp
   * and density of the LED strip.
   *
   * The largest LED matrix fully displayed on the lamp taken as an XY screen
   * display is thus of width \p maxWidth and height \p maxHeight leaving out
   * some "outside" of the default display size.
   *
   * Equal to \p stripYCoordinates (floor) if LampTypes::indexable or else 22
   */
  static constexpr uint16_t maxHeight = _height;

  /// Height as a precise floating point number, equal to \p stripYCoordinates
  static constexpr float maxHeightFloat = _fheight;

  /// Larger height, taken as the absolute maximum Y coordinate, overflowing
  static constexpr uint16_t maxOverflowHeight = maxHeight + 1;

  /// \private Exact visual (X,Y) shift for each row of LED rolled around lamp
  static constexpr float shiftPerTurn = _fwidth - floor(_fwidth - 0.0001);

  /// \private Fixed "period" of the (X,Y) shift for each row (set at 2)
  static constexpr uint16_t shiftPeriod = 2;

  /// (while shifting every shiftPeriod, we have a residue accumulating)
  static constexpr float _invShiftResidue = shiftPeriod * (_fwidth - floor(_fwidth - 0.0001));

  /// \private Approximate (broken) visual coordinate X-shift every \p shiftResidue rows
  static constexpr uint16_t shiftResidue = 100.0 / abs(100.0 * _invShiftResidue - 100.0);

  /// \private All **exact** "residue" / amount of X-shift given the Y coordinate
  static constexpr auto allResiduesY = details::computeResidues<maxOverflowHeight>(_fwidth);

  /// \private Is row at Y coordinate slightly longer than \p maxWidth or not?
  static constexpr auto allDeltaResiduesY = details::computeDeltaResidues<maxOverflowHeight>(_fwidth);

  /// \private Return **total** exact accumulated X-shift residue, accross all previous rows
  static constexpr auto extraShiftResiduesY = details::computeExtraShiftResidues<maxOverflowHeight>(_fwidth);

  /// \private Last (final) total X-shift at the end, all row shifts together
  static constexpr int extraShiftTotal = extraShiftResiduesY[maxOverflowHeight - 1];

  /// real radius of the lamp body
  static constexpr float lampBodyRadius_mm = _lampBodyRadius_mm;

  /// real size of the led strip in use
  static constexpr float ledStripWidth_mm = _ledStripWidth_mm;
  /// Copy the led strip lenght
  static constexpr float ledStripLength_mm = _ledStripLength_mm;

  /// number of led per meters of strip used
  static constexpr float ledByMeter = _ledByMeter;

  /// Number of leds per one turn of led strip
  static constexpr float ledSize_mm = 1000.0f / ledByMeter;
  /// Computation of the lamp body circumpherence
  static constexpr float lampBodyCircumpherence_mm = c_TWO_PI * lampBodyRadius_mm;
  /// Computation of the led count per turns
  static constexpr float ledPerTurns = lampBodyCircumpherence_mm / ledSize_mm;
  /// Computation of the lamp height
  static constexpr float lampHeight_mm = ledStripWidth_mm * ledCount / ledPerTurns;

  /** \brief (indexable) Number of color buffers available for direct access
   *
   * Equal to \p stripNbBuffers if LampTypes::indexable or else 2
   */
  static constexpr uint8_t nbBuffers = _nbBuffers;

  //
  // public helpers
  //

  /** \brief (indexable) Return a led count in 0-ledCount scaled by \p scale
   *
   * Supports:
   *    - from float (0-1) to count (0-ledCount)
   *    - from uint8_t (0-255) to count (0-ledCount)
   */
  template<typename T> static constexpr LMBD_INLINE uint16_t toLedCount(T scale)
  {
    if constexpr (std::is_same_v<T, float>)
    {
      assert(scale <= 1.0 && "scale is 0-1");
      return ledCount * scale;
    }
    else if constexpr (std::is_same_v<T, uint8_t>)
    {
      uint32_t scaled = ledCount * scale;
      return scaled / 256;
    }
    else
    {
      static_assert(std::is_same_v<T, std::false_type>, "Invalid type, either float or uint8_t required!");
      return 0;
    }
  }

  //
  // public API
  //

  /** \brief Clear lamp to a clean state
   *
   * If LampTy::flavor is LampTypes::indexable then:
   *  - clear LED strip with black pixels
   *
   * Or else, for interoperability:
   *  - does nothing
   */
  void LMBD_INLINE clear()
  {
    if constexpr (flavor == LampTypes::indexable)
    {
      for (uint16_t i = 0; i < ledCount; ++i)
      {
        setPixelColor(i, colors::Black);
      }
    }
    else
    {
      // (this is optimized out, and is essentially no-op for other flavors)
      assert(true);
    }
  }

  /** \brief blip the power gate for set time
   *
   * If LampTy::flavor is LampTypes::indexable then:
   *  - clear LED strip with black pixels
   * Else
   *  - disable output power for a duration
   */
  void LMBD_INLINE blip(const uint32_t duration)
  {
    if constexpr (flavor == LampTypes::indexable)
    {
      // disable strip temporarily
      // should be reactivated by the manager
      tempBrightness(0);
    }
    else
    {
      component::outputPower::blip(duration);
    }
  }

  /**
   * \brief Cancel the ongoing blip, if any
   */
  void LMBD_INLINE cancel_blip() const { return component::outputPower::cancel_blip(); }

  /**
   * \brief return true if the output is in a blip state
   */
  bool LMBD_INLINE is_bliping() const { return component::outputPower::is_bliping(); }

  /** \brief Set brightness of the lamp
   *
   * Several behaviors:
   *  - by default, do not call user callbacks to avoid re-entry
   *  - by default, do call global brightness update handler (see brightness_handle.h)
   *  - by default, do NOT save brightness using "previous_brightness_update"
   *  - also set the brightness in underlying strip object, if necessary
   *
   * Thus:
   *  - if \p skipCallbacks is false, do call user callbacks w/ re-entry risks
   *  - if \p skipUpdateBrightness is true, only set strip object brightness,
   *    or do nothing if LampTy::flavor is not LampTypes::indexable
   *  - if \p updateSavedBrightess is true, save brightness and next time
   *    user navigate brightness, use it as starting point (see tempBrightness)
   *
   * Note that calls to `logic::brightness::update_brightness` are throttled to once
   * in every 50ms to avoid freezing user brightness navigation.
   *
   * Note that \p skipUpdateBrightness implies \p skipCallbacks implicitly
   */
  void LMBD_INLINE setBrightness(const brightness_t newBrightness,
                                 const bool skipCallbacks = true,
                                 const bool skipUpdateBrightness = false,
                                 const bool updateSavedBrightess = false)
  {
    assert((skipCallbacks || !skipUpdateBrightness) && "implicit callback skip!");

    // invalid call, fallback to enforcing
    if (newBrightness > ::lampda::brightness::absoluteMaximumBrightness)
    {
      enforce_internal_brightness_limits();
      return;
    }

    // force update if we are getting lower and lower
    if (!skipUpdateBrightness or newBrightness > getMaxBrightness())
    {
      // store the new temporary
      temporary_brightness = min<brightness_t>(newBrightness, getMaxBrightness());

      uint32_t last = logic::brightness::when_last_update_brightness();
      if ((this->now - last) > brightnessDurationMs)
        logic::brightness::update_brightness(temporary_brightness, skipCallbacks);
    }
    // if necessary, update the saved version
    if (updateSavedBrightess)
    {
      saved_brightness = min<brightness_t>(static_cast<brightness_t>(temporary_brightness), getMaxBrightness());
    }

    // USE THE BRIGHTNESS VALUE AFTER THE UPDATE
    // brightness can be limited by the system, so do not use the raw brightness
    const auto trueNewBrightness = logic::brightness::get_brightness();

    if constexpr (flavor == LampTypes::indexable)
    {
#ifndef LMBD_LAMP_TYPE__INDEXABLE
      static constexpr uint8_t minimumAllowedBrightness = 5;
#else
      static constexpr uint8_t minimumAllowedBrightness = ::lampda::minimumAllowedBrightness_8;
#endif
      using curve_t = common::curves::LinearCurve<brightness_t, uint8_t>;
      static curve_t brightnessCurve = ::lampda::common::curves::make_linear_curve(
              curve_t::point_t {0, minimumAllowedBrightness},
              curve_t::point_t {::lampda::brightness::absoluteMaximumBrightness, 255});

      /// @warning: this is actually heavy to run
      strip.setBrightness(brightnessCurve.sample(trueNewBrightness));
    }

    if constexpr (flavor == LampTypes::simple)
    {
      const auto trueMaxBrightness = logic::brightness::get_max_brightness();

      // This is kind of a hack to detect that the user did this call
      // using the known user call signature
      const bool isUserCall = skipCallbacks and skipUpdateBrightness and not updateSavedBrightess;

      // display an output blip on max brightness reached
      if (isUserCall and trueNewBrightness >= trueMaxBrightness)
      {
        component::outputPower::blip(50); // blip
      }

      using curve_t = common::curves::ExponentialCurve<brightness_t, uint16_t>;
      static curve_t brightnessCurve(
              curve_t::point_t {0, stripInputMinVoltage_mV},
              curve_t::point_t {::lampda::brightness::absoluteMaximumBrightness, stripInputMaxVoltage_mV},
              1.0);

      component::outputPower::write_voltage(round(brightnessCurve.sample(trueNewBrightness)));
    }
  }

  /// Special call to update the internal brightness values to the system brightness
  void align_internal_to_system_brightness()
  {
    saved_brightness = min<brightness_t>(logic::brightness::get_saved_brightness(), getMaxBrightness());
    temporary_brightness = saved_brightness;
  }

  /// Enforce the brightness limits, if getMaxBrightness changed. Will call \ref setBrightness
  void enforce_internal_brightness_limits()
  {
    const auto maxAllowedBrightness = getMaxBrightness();
    const brightness_t new_saved_brightness =
            min<brightness_t>(static_cast<brightness_t>(saved_brightness), maxAllowedBrightness);
    const brightness_t new_temporary_brightness =
            min<brightness_t>(static_cast<brightness_t>(temporary_brightness), maxAllowedBrightness);

    const bool isChanged = new_saved_brightness != saved_brightness or new_temporary_brightness != temporary_brightness;
    if (isChanged)
    {
      saved_brightness = new_saved_brightness;
      temporary_brightness = new_temporary_brightness;

      setBrightness(temporary_brightness);
    }
  }

  /**
   * \brief Return the actual allowed maximum brightness
   */
  brightness_t LMBD_INLINE getMaxBrightness() const { return logic::brightness::get_max_user_brightness(); }

  /**
   * \brief Temporarily set brightness, without affecting brightness navigation
   *
   * Skip callbacks.
   *
   * Set brightness, without affecting internal brightness navigation state,
   * which imply that next time an user increases / lowers brightness, it
   * starts again from another internal "previously saved" brightness.
   *
   * Equivalent to ``setBrightness(true, false, false)``
   */
  void LMBD_INLINE tempBrightness(const brightness_t brightness)
  {
    brightness_t current = getBrightness();
    if (current != brightness)
      setBrightness(brightness, true, false, false);
  }

  /**
   * \brief Jump to brightness, affecting the next brightness navigation
   *
   * Skip callbacks.
   *
   * Set brightness, affecting internal brightness navigation state,
   * which imply that next time an user increases / lowers brightness, it
   * starts again from the provided brightness.
   *
   * Equivalent to ``setBrightness(true, false, true)``
   */
  void LMBD_INLINE jumpBrightness(const brightness_t brightness) { setBrightness(brightness, true, false, true); }

  /**
   * \brief Get brightness of the lamp
   *
   * If \p readPreviousBrightness is true, return the internally saved
   * brightness state, used for user navigation of brightness.
   */
  brightness_t LMBD_INLINE getBrightness(const bool readPreviousBrightness = false)
  {
    if (readPreviousBrightness)
      return saved_brightness;
    else
      return temporary_brightness;
  }

  /// Alias for ``getBrightness(true)``
  brightness_t LMBD_INLINE getSavedBrightness() { return getBrightness(true); }

  /// Reset brightness to internal saved brightness, skip callbacks
  void LMBD_INLINE restoreBrightness()
  {
    const brightness_t current = getBrightness();
    const brightness_t saved = getSavedBrightness();

    if (current != saved)
      setBrightness(saved, true, false, false);
  }

  /** \brief Fade currently displayed content by \p fadeBy units
   *
   * If LampTy::flavor is LampTypes::indexable then:
   *  - do not change brightness, only scale color of individual LEDs
   *
   * Or else, for other flavors of lamp:
   *  - reduce brightness by \p fadeBy floored at zero
   */
  void LMBD_INLINE fadeToBlackBy(uint8_t fadeBy)
  {
    if constexpr (flavor == LampTypes::indexable)
    {
      if (fadeBy == 0)
        return; // optimization - no scaling to apply

      for (uint16_t i = 0; i < ledCount; ++i)
      {
        const uint32_t c = getPixelColor(i);
        setPixelColor(i, colors::fade(c, 255 - fadeBy));
      }
    }
    else
    {
      uint8_t brightness = getBrightness();
      brightness = (brightness < fadeBy) ? 0 : brightness - fadeBy;
      setBrightness(brightness);
    }
  }

  /** \brief Blur currently displayed content by \p blurBy units
   * /!\ Only applied along the strip, not in 2D /!\
   *
   * If LampTy::flavor is LampTypes::indexable then:
   *  - do not change brightness, only scale color of individual LEDs
   *
   * Or else, for other flavors of lamp:
   *  - blue colors by \p blurBy floored at zero
   */
  void LMBD_INLINE blur(uint8_t blurBy)
  {
    if (blurBy == 0)
      return; // optimization: 0 means "don't blur"
    uint8_t keep = 255 - blurBy;
    uint8_t seep = blurBy >> 1;

    uint32_t carryover = 0;
    for (unsigned i = 0; i < ledCount; i++)
    {
      uint32_t cur = getPixelColor(i);
      uint32_t c = cur;
      uint32_t part = colors::fade<false>(c, seep);
      cur = colors::add<true>(colors::fade<false>(c, keep), carryover);
      if (i > 0)
      {
        c = getPixelColor(i - 1);
        setPixelColor(i - 1, colors::add<true>(c, part));
      }
      setPixelColor(i, cur);
      carryover = part;
    }
  }

  //
  // public API (indexable-only)
  //

  /** \brief (indexable) Fill lamp with target color, from start to end
   *
   * - See toLedCount() to set \p start and \p end
   * - See modes::colors::fromRGB() to set \p color
   */
  void LMBD_INLINE fill(uint32_t color, uint16_t start, uint16_t end)
  {
    if constexpr (flavor == LampTypes::indexable)
    {
      assert(start <= ledCount && "invalid start parameter");
      assert(end <= ledCount && "invalid end parameter");

      for (uint16_t I = start; I < end; ++I)
      {
        setPixelColor(I, color);
      }
    }
    else
    {
      assert(false && "unsupported");
    }
  }

  /** \brief (indexable) Fill lamp with target color, from start to end. Apply a mask to display leds
   *
   * - See toLedCount() to set \p start and \p end
   * - See modes::colors::fromRGB() to set \p color
   */
  void LMBD_INLINE fill(uint32_t color, uint16_t start, uint16_t end, const BufferTy& shouldDisplay)
  {
    if constexpr (flavor == LampTypes::indexable)
    {
      assert(start <= ledCount && "invalid start parameter");
      assert(end <= ledCount && "invalid end parameter");

      for (uint16_t I = start; I < end; ++I)
      {
        const uint8_t blendValue = min<uint32_t>(shouldDisplay[I], UINT8_MAX);
        setPixelColor(I, colors::blend<uint8_t>(0, color, blendValue));
      }
    }
    else
    {
      assert(false && "unsupported");
    }
  }

  /** \brief (indexable) Fill lamp with target color
   *
   * See modes::colors::fromRGB() to set \p color
   */
  void LMBD_INLINE fill(uint32_t color) { fill(color, 0, ledCount); }

  /** \brief (indexable) Fill lamp with target color, with a mask
   *
   * See modes::colors::fromRGB() to set \p color
   */
  void LMBD_INLINE fill(uint32_t color, const BufferTy& shouldDisplay) { fill(color, 0, ledCount, shouldDisplay); }

  /** \brief (indexable) Fill lamp with target palette, from start to end
   *
   * - See toLedCount() to set \p start and \p end
   * - See modes::colors::PaletteTy to set \p palette
   */
  void LMBD_INLINE fill(const colors::PaletteTy& palette, uint16_t start, uint16_t end)
  {
    if constexpr (flavor == LampTypes::indexable)
    {
      assert(start < ledCount && "invalid start parameter");
      assert(end <= ledCount && "invalid end parameter");

      for (uint16_t I = start; I < end; ++I)
      {
        // map index to [0; 255]
        const auto color = colors::from_palette<false, uint8_t>(I / static_cast<float>(ledCount) * 255, palette);
        setPixelColor(I, color);
      }
    }
    else
    {
      assert(false && "unsupported");
    }
  }

  /** \brief (indexable) Fill lamp with target palette
   * - See modes::colors::PaletteTy to set \p palette
   */
  void LMBD_INLINE fill(const colors::PaletteTy& palette) { fill(palette, 0, ledCount); }

  /** \brief (indexable) Set the n-th LED color
   *
   * See modes::fromRGB() to set \p color
   */
  void LMBD_INLINE setPixelColor(uint16_t n, uint32_t color)
  {
    if constexpr (flavor == LampTypes::indexable)
    {
      if (config.skipFirstLedsForEffect && n < config.skipFirstLedsForAmount)
      {
        return;
      }

      assert(n < ledCount && "invalid LED index");
      strip.setPixelColor(n, color);
    }
    else
    {
      assert(false && "unsupported");
    }
  }

  /** \brief (indexable) Get the n-th LED color
   */
  uint32_t LMBD_INLINE getPixelColor(uint16_t n)
  {
    if constexpr (flavor == LampTypes::indexable)
    {
      if (config.skipFirstLedsForEffect && n < config.skipFirstLedsForAmount)
      {
        return 0;
      }

      assert(n < ledCount && "invalid LED index");
      return strip.getPixelColor(n);
    }
    else
    {
      assert(false && "unsupported");
    }
  }

  /** \brief (indexable) Set the X,Y-th LED color
   *
   * See modes::fromRGB() to set \p color
   */
  void LMBD_INLINE setPixelColorXY(uint16_t X, uint16_t Y, uint32_t color) { setPixelColor(to_strip(X, Y), color); }

  /** \brief (indexable) Given X,Y coordinate, return a corresponding LED index
   *
   * Uses modes::to_strip as implementation (both function are equivalent)
   */
  static uint16_t LMBD_INLINE fromXYtoStripIndex(uint16_t X, uint16_t Y) { return to_strip(X, Y); }

  /** \brief (indexable) Given a LED index, return a corresponding X,Y value
   *
   * Uses modes::strip_to_XY as implementation (both function are equivalent)
   */
  static XYTy LMBD_INLINE fromStripIndexToXY(uint16_t N) { return strip_to_XY(N); }

  /** \brief Get a reference to the \p bufIdx temporary buffer
   *
   * These buffers can be used for computations by the active mode, but their
   * content may be erased if the mode is reset or if used elsewhere in code.
   */
  template<uint8_t bufIdx = 0> BufferTy& LMBD_INLINE getTempBuffer()
  {
    static_assert(bufIdx < nbBuffers, "bufIdx must be lower than nbBuffers");
    BufferTy& buffer = strip._buffers[bufIdx];
    return buffer;
  }

  /**
   * \brief Copy a source buffer at \p srcBufIdx to another buffer at \p dstBufIdx
   *
   * These buffers can be used for computations by the active mode, but their
   * content may be erased if the mode is reset or if used elsewhere in code.
   */
  template<uint8_t dstBufIdx, uint8_t srcBufIdx> void LMBD_INLINE copyBuffer()
  {
    static_assert(srcBufIdx < nbBuffers, "srcBufIdx must be lower than nbBuffers");
    static_assert(dstBufIdx < nbBuffers, "dstBufIdx must be lower than nbBuffers");

    strip._buffers[dstBufIdx] = strip._buffers[srcBufIdx];
  }

  /** \brief Fill temporary buffer \p bufIdx with given \p value
   *
   * Equivalent to ``getTempBuffer().fill(value)``
   */
  template<uint8_t bufIdx = 0, typename T> void LMBD_INLINE fillTempBuffer(const T& value)
  {
    getTempBuffer<bufIdx>().fill(value);
  }

  /** \brief (indexable) Display \p bufIdx temporary buffer as LED colors
   *
   * This ``memcpy`` the selected buffer to the internal strip color buffer.
   */
  template<uint8_t bufIdx = 0> void setColorsFromBuffer()
  {
    static_assert(sizeof(BufferTy) == sizeof(strip._colors));
    const BufferTy& buffer = getTempBuffer<bufIdx>();
    if (config.skipFirstLedsForEffect)
    {
      uint16_t Idx = config.skipFirstLedsForAmount;
      uint16_t Sz = sizeof(strip._colors) - Idx * sizeof(uint32_t);
      memcpy(&strip._colors[Idx], &buffer[Idx], Sz);
    }
    else
    {
      memcpy(strip._colors, buffer.data(), sizeof(strip._colors));
    }
  }

  /**
   * \brief Mix two colors from a buffer
   * \param[in] phase Between 0 and 1, the gradient to apply
   */
  template<uint8_t dstBufIdx = 0, uint8_t srcBufIdx = 1> void setColorsFromMixedBuffers(float phase)
  {
    static_assert(sizeof(BufferTy) == sizeof(strip._colors));
    const BufferTy& dstBuf = getTempBuffer<dstBufIdx>();
    const BufferTy& srcBuf = getTempBuffer<srcBufIdx>();

    uint16_t start = 0, end = srcBuf.size();
    if (config.skipFirstLedsForEffect)
    {
      start = config.skipFirstLedsForAmount;
    }

    for (uint16_t I = start; I < end; ++I)
    {
      COLOR src, dst;
      src.color = srcBuf[I];
      dst.color = dstBuf[I];
      strip._colors[I].color = utils::get_gradient(src.color, dst.color, phase);
    }
  }

  /** \brief (indexable) Display \p bufIdx temporary buffer, but reversed
   */
  template<uint8_t bufIdx = 0> void setColorsFromBufferReversed(bool skipLastLine)
  {
    static_assert(sizeof(BufferTy) == sizeof(strip._colors));
    const BufferTy& buffer = getTempBuffer<bufIdx>();

    uint16_t start = 0, end = buffer.size();
    if (config.skipFirstLedsForEffect)
    {
      start = config.skipFirstLedsForAmount;
    }

    if (skipLastLine)
    {
      end = maxWidth * maxHeight;
    }

    for (uint16_t I = 0, J = start; I < end - start; ++I, ++J)
    {
      strip._colors[J].color = buffer[end - start - I - 1];
    }
  }

  /** \brief (indexable) Copy all current LEDs color to \p bufIdx temp. buffer
   *
   * If \p forceFullRead is True, also copy skipped content.
   */
  template<uint8_t bufIdx = 0, bool forceFullRead = false> void getColorsToBuffer()
  {
    static_assert(sizeof(BufferTy) == sizeof(strip._colors));

    BufferTy& buffer = getTempBuffer<bufIdx>();
    if (!forceFullRead && config.skipFirstLedsForEffect)
    {
      uint16_t Idx = config.skipFirstLedsForAmount;
      uint16_t Sz = sizeof(strip._colors) - Idx * sizeof(uint32_t);

      buffer.fill(0);
      memcpy(&buffer[Idx], &strip._colors[Idx], Sz);
    }
    else
    {
      memcpy(buffer.data(), strip._colors, sizeof(strip._colors));
    }
  }

  /**
   * \brief Return the an object containing sound analysis data
   */
  component::microphone::SoundStruct& LMBD_INLINE get_sound_struct()
  {
    return component::microphone::get_sound_characteristics();
  }

  /// Define a localy consistant saved brightness. Should be similar
  volatile brightness_t saved_brightness;
  /// Define a localy consistant temporary brightness
  volatile brightness_t temporary_brightness;

  /** \brief (physical) The "now" on milliseconds, updated just before loop.
   *
   * This value is \p get_time_ms() called once and used as basis for \p tick
   * and may wrap around every three weeks of functioning.
   */
  volatile const uint32_t now;

  /** \brief (physical) Tick number, ever-increasing every frameDurationMs
   *
   * This value increments 83.3 times per second and is updated once per loop.
   *
   * It is based on the internal board clock, that counter is time-based and
   * best used to build animations, but intermediary values may be skipped.
   */
  volatile const uint32_t tick;

  /** \brief (physical) Raw frame count, incremented at an undefined rate
   *
   * This value increments everytime the loop method is called, and its rate
   * may vary depending on hardware and load. If used to build animations, this
   * may cause stutters or visible slowdowns during loads.
   */
  volatile const uint32_t raw_frame_count;
};

} // namespace lampda::modes::hardware

namespace lampda::modes {

/// \brief Convert \p x and \p y coordinates to a linear position on strip
static constexpr uint16_t to_strip(uint16_t x, uint16_t y)
{
  // maxHeight is the last "full" row and maxOverflowHeight is truncated row
  //  -> user max use to_strip(x, maxOverflowHeight) to set truncated row
  if (y >= hardware::LampTy::maxOverflowHeight)
  {
    y = hardware::LampTy::maxOverflowHeight - 1;
  }

  // if row is longer (because next row gets a shift) use maxOverflowWidth
  if (hardware::LampTy::allDeltaResiduesY[y])
  {
    if (x >= hardware::LampTy::maxOverflowWidth)
    {
      x = hardware::LampTy::maxOverflowWidth - 1;
    }

    // if row is aligned to XY maxWidth/maxHeight matrix, use maxWidth instead
  }
  else if (x >= hardware::LampTy::maxWidth)
  {
    x = hardware::LampTy::maxWidth - 1;
  }

  // final result is capped by the "real" LED count of the strip
  uint16_t n = x + y * hardware::LampTy::maxWidth + hardware::LampTy::allResiduesY[y];
  if (n >= hardware::LampTy::ledCount)
    n = hardware::LampTy::ledCount - 1;
  return n;
}

/// \brief Convert a \p n index on the LED strip to a matching XY coordinate
static constexpr XYTy strip_to_XY(uint16_t n)
{
  // (saturates N to ledCount)
  if (n >= hardware::LampTy::ledCount)
    n = hardware::LampTy::ledCount - 1;

  uint16_t y = 0;
  while (y * hardware::LampTy::maxWidth + hardware::LampTy::allResiduesY[y] <= n)
    y += 1;

  if (y == 0)
    return {0, 0};
  y -= 1;

  uint16_t x = n - y * hardware::LampTy::maxWidth - hardware::LampTy::allResiduesY[y];
  return {x, y};
}

/**
 * \brief Convert a strip led index to a 3D helix coordinate.
 * \param[in] n Index of the led in the strip. If will be constraint to the lamp body
 * \return Coordinates of the led in the 3D world (mm)
 */
static constexpr HelixXYZTy strip_to_helix(int16_t n)
{
  if (n > hardware::LampTy::ledCount)
    return HelixXYZTy {0.0, 0.0, 0.0};

  return strip_to_helix_unconstraint(n);
}

/**
 * \brief Convert a led index to an helix height coordinate.
 * \param[in] n Index of the led in the strip, unconstraint to the lamp body.
 * \return The height if the pixel, in mm.
 */
static constexpr float to_helix_z(const int16_t n)
{
  return -hardware::LampTy::ledStripWidth_mm * n / hardware::LampTy::ledPerTurns;
}

/**
 * \brief Convert a strip led index to a 3D helix coordinate.
 * \param[in] n Index of the led in the strip, unconstraint to the lamp body.
 * \return Coordinates of the led in the 3D world (mm)
 */
static constexpr HelixXYZTy strip_to_helix_unconstraint(const int16_t n)
{
  return HelixXYZTy {hardware::LampTy::maxWidthFloat * cos_t(n / hardware::LampTy::ledPerTurns * c_TWO_PI),
                     hardware::LampTy::maxWidthFloat * sin_t(n / hardware::LampTy::ledPerTurns * c_TWO_PI),
                     to_helix_z(n)};
}

/**
 * \brief Return true id the given led index exists on the strip.
 * \param[in] n Index of the led in the strip.
 */
static constexpr bool is_led_index_valid(const int16_t n) { return n >= 0 and n < hardware::LampTy::ledCount; }

/**
 * \brief Return true id the given coordinates exists on the strip.
 * This function also checks the bounds using the observation angle, as the strip is an helix.
 * \param[in] angle_rad Angle in radians of the pixel.
 * \param[in] z_mm height, in mm. Height in this coordinate system is negative.
 */
static constexpr bool is_lamp_coordinate_out_of_bounds(const float angle_rad, const float z_mm)
{
  return not is_led_index_valid(to_led_index_no_bounds(angle_rad, z_mm));
}

/**
 * \brief Convert a cylindrical world coordinate to a led index
 * \param[in] angle_rad Angle in radians of the pixel.
 * \param[in] z_mm height, in mm. Height in this coordinate system is negative.
 * \return The index of the led, constrained to a valid index in the strip.
 */
static constexpr uint16_t to_led_index(const float angle_rad, const float z_mm)
{
  constexpr uint16_t maxZCoordinate =
          floor(-to_helix_z(hardware::LampTy::ledCount) / hardware::LampTy::ledStripWidth_mm);

  // snip Z per possible lines
  uint16_t zIndex = floor(-z_mm / hardware::LampTy::ledStripWidth_mm);
  if (zIndex < 0.0)
    zIndex = 0.0;
  if (zIndex > maxZCoordinate)
    zIndex = maxZCoordinate;

  // indexing around the led turn
  const float angularPosition = wrap_angle(angle_rad) / c_TWO_PI * hardware::LampTy::maxWidthFloat;

  // convert to led index (approx)
  int16_t ledIndex = round(angularPosition + zIndex * hardware::LampTy::maxWidthFloat);
  if (ledIndex < 0)
    ledIndex = round(angularPosition + (zIndex + 1) * hardware::LampTy::maxWidthFloat);
  if (ledIndex >= hardware::LampTy::ledCount)
    ledIndex = round(angularPosition + (zIndex - 1) * hardware::LampTy::maxWidthFloat);

  if (ledIndex < 0)
    return 0;
  if (ledIndex >= hardware::LampTy::ledCount)
    return hardware::LampTy::ledCount - 1;
  return ledIndex;
}

/**
 * \brief Convert a cylindrical world coordinate to a led index
 * \param[in] angle_rad Angle in radians of the pixel.
 * \param[in] z_mm height, in mm. Height in this coordinate system is negative.
 * \return The index of the led. It is not necessarly a valid index.
 */
static constexpr int16_t to_led_index_no_bounds(const float angle_rad, const float z_mm)
{
  // snip Z per possible lines
  const int16_t zIndex = floor(-z_mm / hardware::LampTy::ledStripWidth_mm);
  // indexing around the led turn
  const float angularPosition = wrap_angle(angle_rad) / c_TWO_PI * hardware::LampTy::maxWidthFloat;

  // convert to led index (approx)
  return round(angularPosition + zIndex * hardware::LampTy::maxWidthFloat);
}

} // namespace lampda::modes

#endif
