BaptisteHudyma/Lamp-Da/src/modes/include/manager_type.hpp

#ifndef MANAGER_TYPE_H
#define MANAGER_TYPE_H

/** \file
 *
 *  \brief modes::ManagerFor and associated definitions
 **/

#include <cstdint>
#include <utility>
#include <tuple>
#include <array>

#include <src/system/logic/alerts.h>
#include <src/system/logic/sun_timers.h>

#include <src/system/utils/assert.h>

#include "src/modes/include/draw/overlay.hpp"

#include "src/modes/include/tools.hpp"
#include "src/modes/include/context_type.hpp"
#include "src/modes/include/default_config.hpp"
#include "src/modes/include/hardware/keystore.hpp"
#include "src/modes/include/hardware/lamp_type.hpp"

namespace lampda::modes {

/// \private Active state is designated by a 32-bit integer
union ActiveIndexTy
{
  struct
  {
    /// the two index below should only be modified by set_active_group & set_active_mode
    uint8_t groupIndex; // group id (as ordered in the manager)
    uint8_t modeIndex;  // mode id (as ordered in its group)
    ///

    uint8_t rampIndex;   // ramp value (as set by the user)
    uint8_t customIndex; // custom (as set by the mode)
  };

  uint32_t rawIndex;

  // static constructors
  //
  static constexpr auto from(const uint8_t* arr)
  {
    ActiveIndexTy index = {arr[0], arr[1], arr[2], arr[3]};
    return index;
  }
  static constexpr auto from(const std::array<uint8_t, 4>& arr) { return ActiveIndexTy::from(arr.data()); }
};

/// \private Contains the logic to handle a fixed-timestep range
template<typename Config> struct RampHandlerTy
{
  using ConfigTy = Config;
  static constexpr uint32_t startPeriod = Config::rampStartPeriodMs;

  // \in stepSpeed how long to wait before incrementing (ms)
  // \in rampSaturates does the ramp saturates, or else wrap around?
  RampHandlerTy(uint32_t stepSpeed, bool rampSaturates = Config::defaultRampSaturates) :
    stepSpeed {stepSpeed},
    rampSaturates {rampSaturates},
    lastTimeMeasured {1000},
    isForward {true},
    animEffect {Config::defaultCustomRampAnimEffect},
    animChoice {Config::defaultCustomRampAnimChoice}
  {
  }

  void LMBD_INLINE reset()
  {
    isForward = true;
    stepSpeed = Config::defaultCustomRampStepSpeedMs;
    rampSaturates = Config::defaultRampSaturates;
    animEffect = Config::defaultCustomRampAnimEffect;
    animChoice = Config::defaultCustomRampAnimChoice;
  }

  void LMBD_INLINE update_ramp(uint8_t rampValue, uint32_t holdTime, auto callback)
  {
    // restart the rampage
    if (holdTime < lastTimeMeasured)
    {
      lastTimeMeasured = holdTime;

      if (holdTime < startPeriod)
      {
        // toggle forward / backward direction
        isForward = !isForward;
        if (rampSaturates)
        {
          if (rampValue == 0)
            isForward = true;
          if (rampValue == 255)
            isForward = false;
        }
      }
      return;
    }

    // count how many step we advanced
    uint32_t lastCounter = lastTimeMeasured / stepSpeed;
    uint32_t nextCounter = holdTime / stepSpeed;
    if (nextCounter <= lastCounter)
      return;

    // apply steps
    for (uint32_t I = 0; I < nextCounter - lastCounter; ++I)
    {
      // increment iff possible
      if (isForward && (!rampSaturates || rampValue < 255))
        rampValue += 1;

      // decrement iff possible
      if (!isForward && (!rampSaturates || rampValue > 0))
        rampValue -= 1;

      // forward value to callback
      callback(rampValue);
    }

    lastTimeMeasured = holdTime;
  }

  uint32_t stepSpeed;
  bool rampSaturates;
  bool animEffect;
  bool animChoice;
  uint32_t lastTimeMeasured;
  bool isForward;
};
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
